MayaPosch/Nucleo-144_mounting/IMG_20210814_223848.jpg

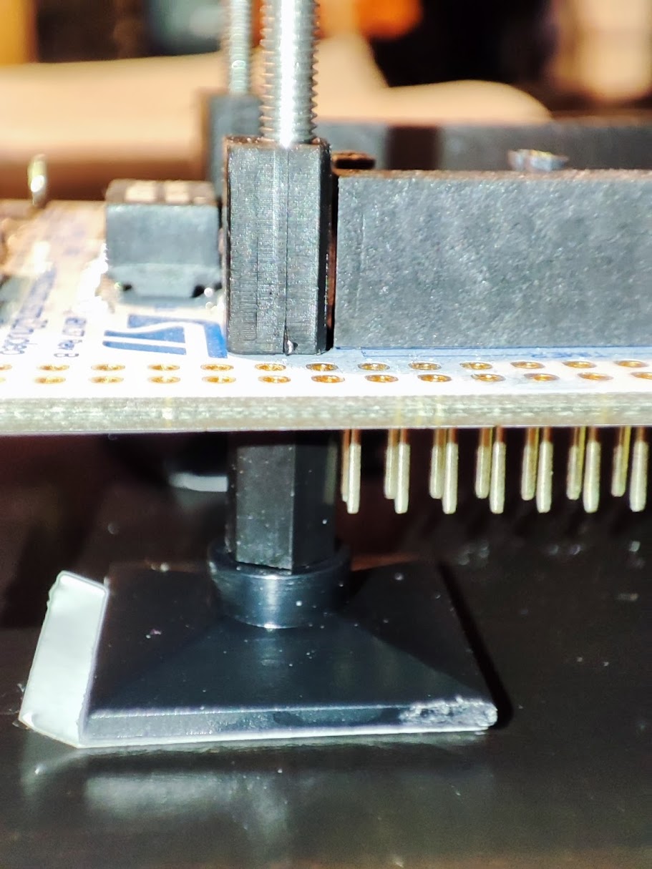
IMG_20210814_223848.jpg
